Stulinaz/STM32F103RB_USB_to_UART_SPI_I2C/firmware/Core/Inc/led_manager.h

#ifndef INC_LED_MANAGER_H_
#define INC_LED_MANAGER_H_

#include "main.h"
#include "buffers_manager.h"
#include "command_process.h"

#define TX_LED_ON_TIME       (uint32_t) 180
#define RX_LED_ON_TIME       (uint32_t) 180
#define LED_ERROR_BLINK_TIME (uint32_t) 250
#define LED_ERROR_DEAD_TIME  (uint32_t) 1500

void LedManager(void);
void USBStatusLed(GPIO_PinState status);
void LedInterfaceSel(comm_interface_t type);
void ErrorCodeSet(uint8_t err_num);
void CommunicationLedVisualize(void);
void LedTest(uint32_t time);

#endif
