Stulinaz/STM32F103RB_USB_to_UART_SPI_I2C/firmware/Core/Inc/sys_definitions.h

#ifndef INC_SYS_DEFINITIONS_H_
#define INC_SYS_DEFINITIONS_H_

/* SYSTEM CLOCK */
#define EXTERNAL_16MHZ

/* IIC */
#define IIC_PULLUP_EXTERNAL
#define I2C_ERROR_VERBOSE

/* IC DRIVER - MIPOT TRZ MODULE */
#define MIPOT_TRX_PROGRAM_ENABLED

/* ACCESSORIES*/
#define TAB         (uint8_t) 0x09
#define CR_         (uint8_t) 0x0D
#define LF_         (uint8_t) 0x0A
#define END_CHAR    '\0'

#endif
